smjacques/Horta-Automatizada-ESDI/imagens/800px-ATMEGA328P-PU.jpg

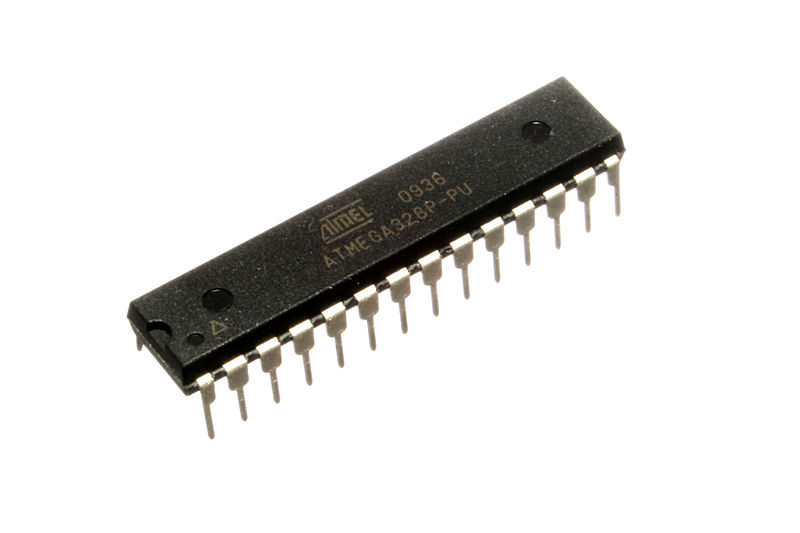
imagens/800px-ATMEGA328P-PU.jpg
