smjacques/Horta-Automatizada-ESDI/imagens/800px-Microchip_PIC24HJ32GP202.jpg

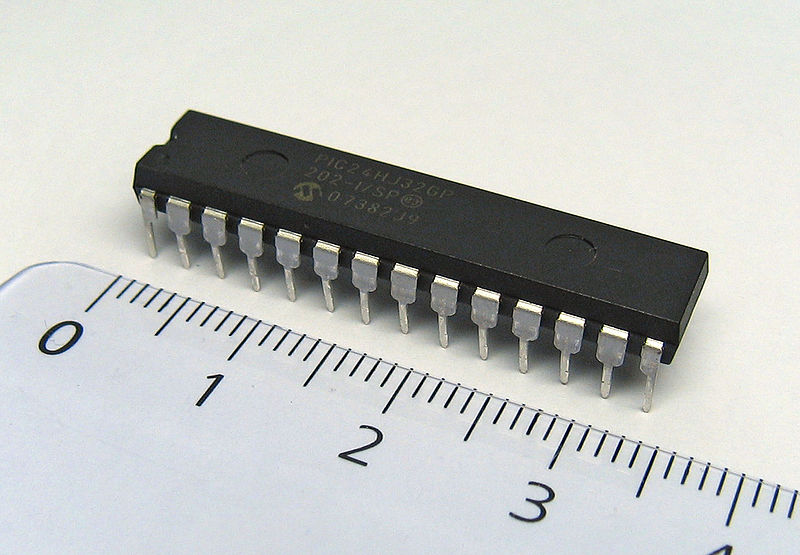
imagens/800px-Microchip_PIC24HJ32GP202.jpg
