smjacques/Horta-Automatizada-ESDI/imagens/2706173_49cf0924.jpg

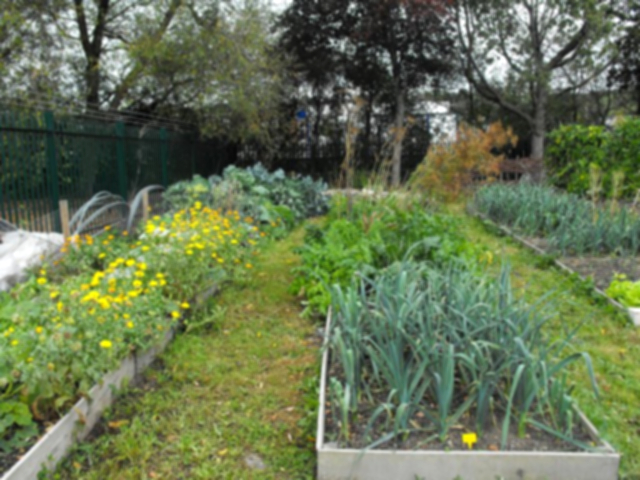
imagens/2706173_49cf0924.jpg
