smjacques/Horta-Automatizada-ESDI/imagens/aexdi.png

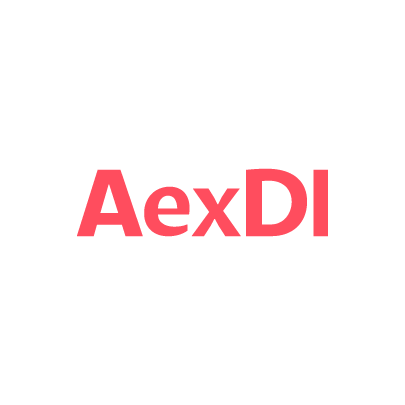
imagens/aexdi.png
