smjacques/Horta-Automatizada-ESDI/imagens/arduino_board.png

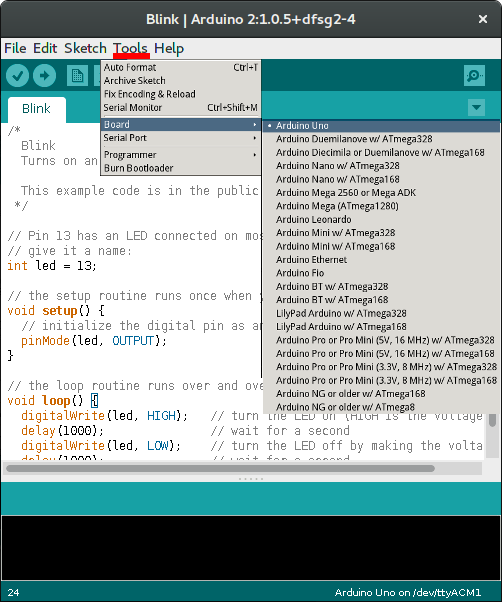
imagens/arduino_board.png
