smjacques/Horta-Automatizada-ESDI/imagens/Arduino_capa.jpg

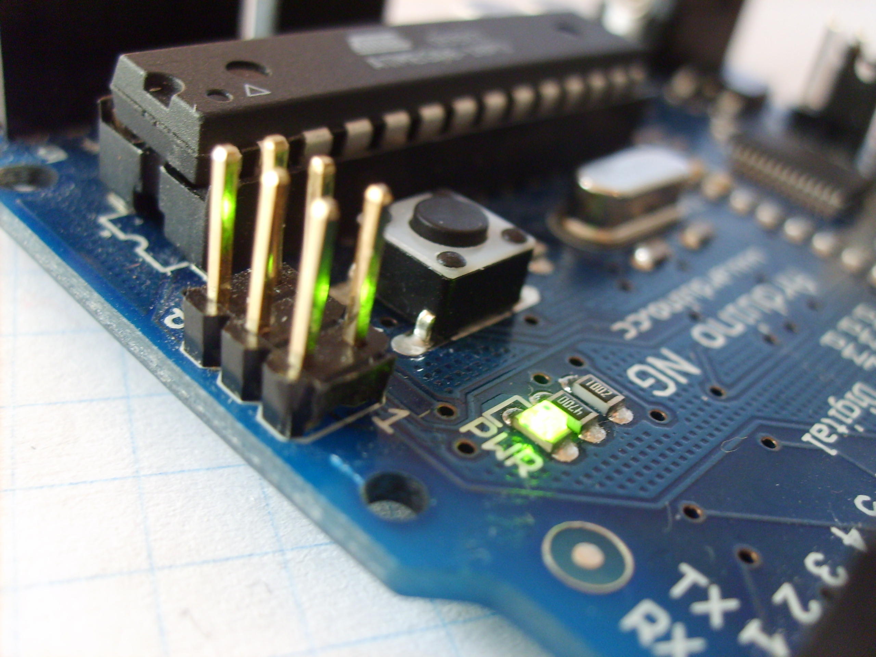
imagens/Arduino_capa.jpg
