smjacques/Horta-Automatizada-ESDI/imagens/Arduino_crystal-1.jpg

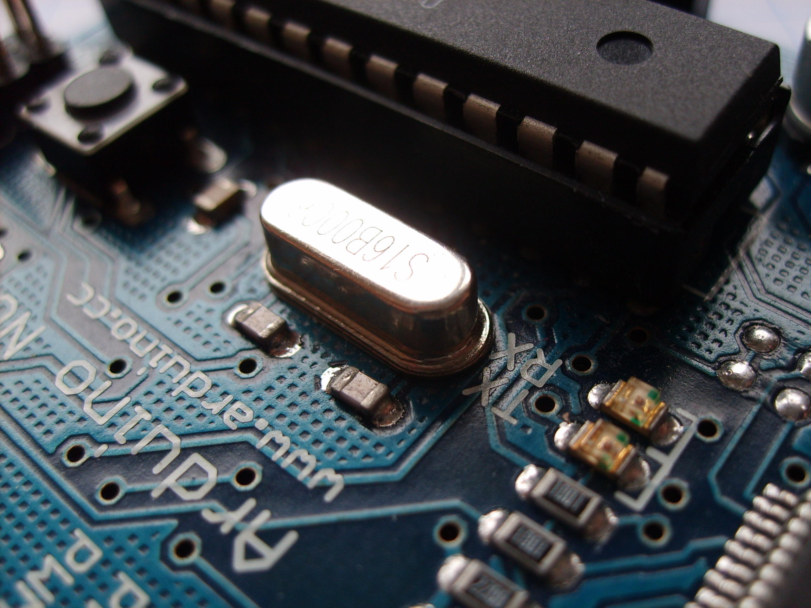
imagens/Arduino_crystal-1.jpg
