smjacques/Horta-Automatizada-ESDI/imagens/arduino_port.png

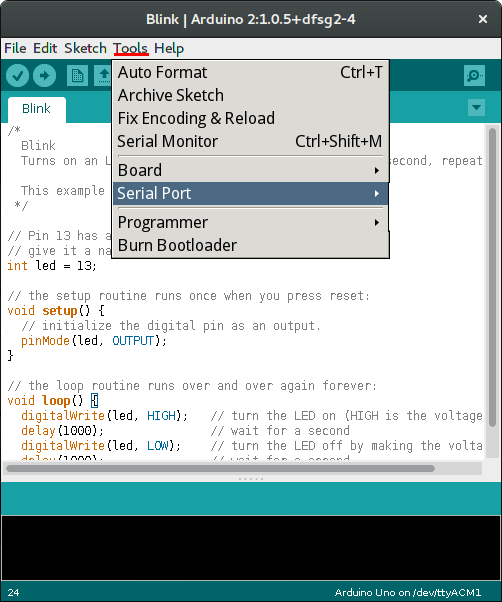
imagens/arduino_port.png
