smjacques/Horta-Automatizada-ESDI/imagens/arduinos.png

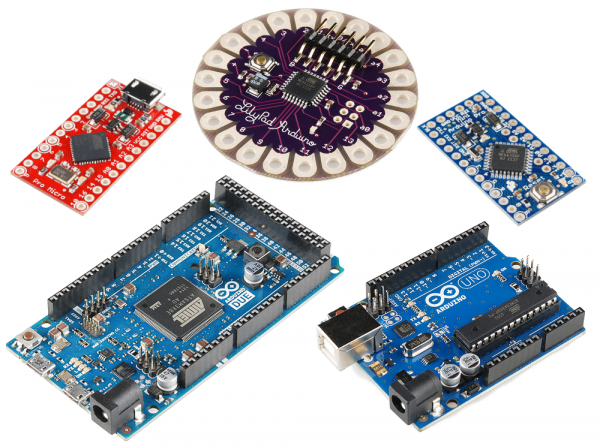
imagens/arduinos.png
