smjacques/Horta-Automatizada-ESDI/imagens/AVR_ATXMEGA_128A1.JPG

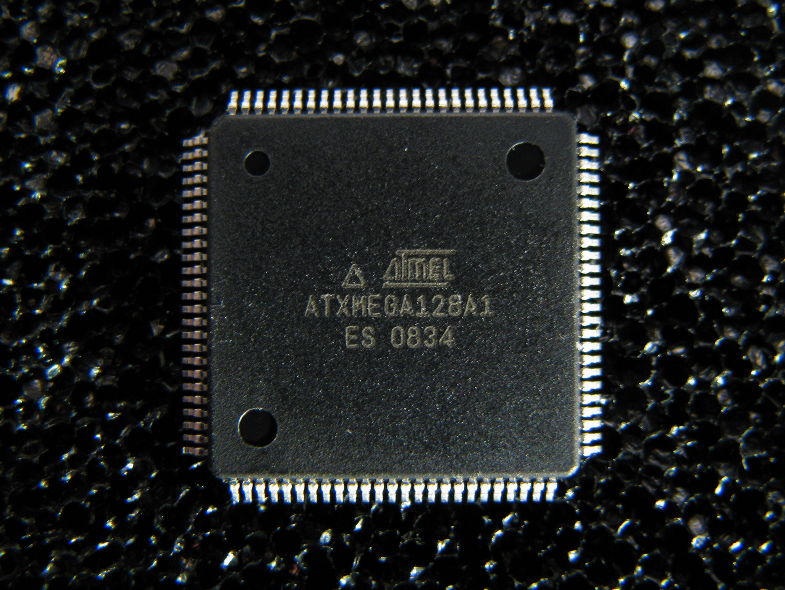
imagens/AVR_ATXMEGA_128A1.JPG
