smjacques/Horta-Automatizada-ESDI/imagens/codigo_de_cores_resistores.png

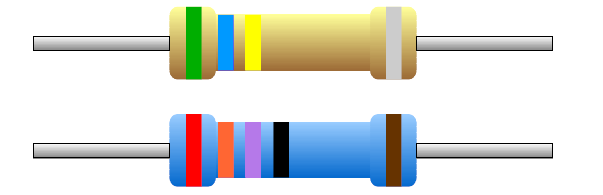
imagens/codigo_de_cores_resistores.png
