smjacques/Horta-Automatizada-ESDI/imagens/esdi.png

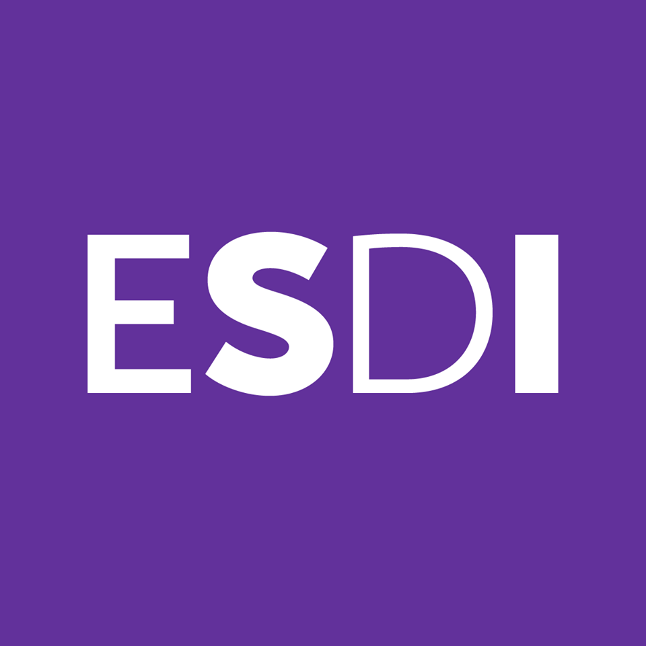
imagens/esdi.png
