smjacques/Horta-Automatizada-ESDI/imagens/green-background-2433829_1920.jpg

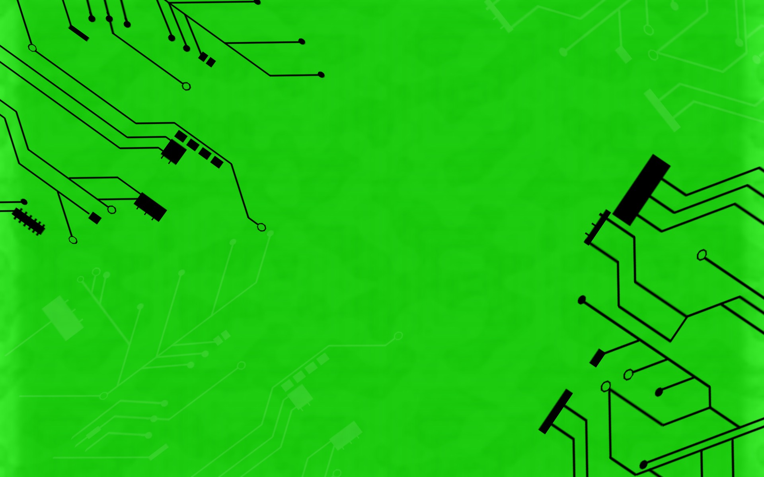
imagens/green-background-2433829_1920.jpg
