smjacques/Horta-Automatizada-ESDI/imagens/IDE.png

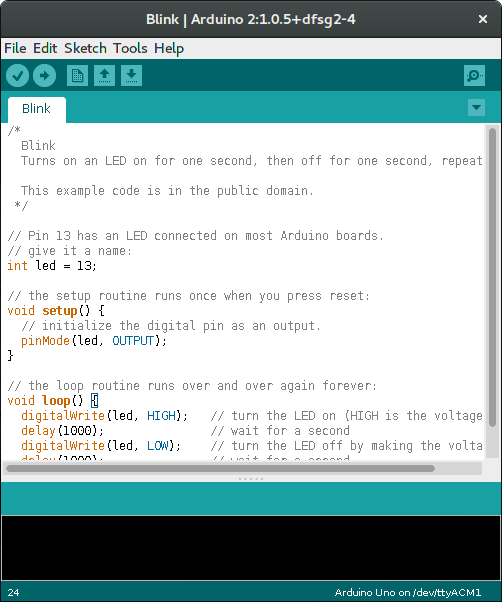
imagens/IDE.png
