smjacques/Horta-Automatizada-ESDI/imagens/images.jpeg

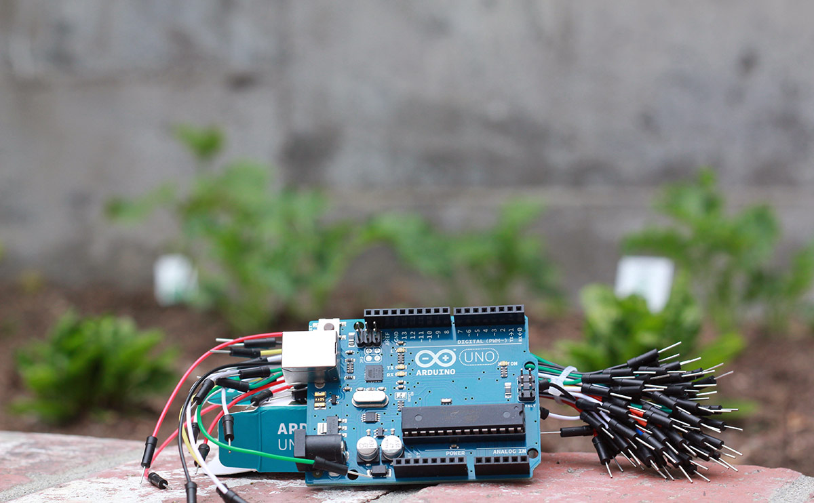
imagens/images.jpeg
