smjacques/Horta-Automatizada-ESDI/imagens/oficina_automatizada_bb.png

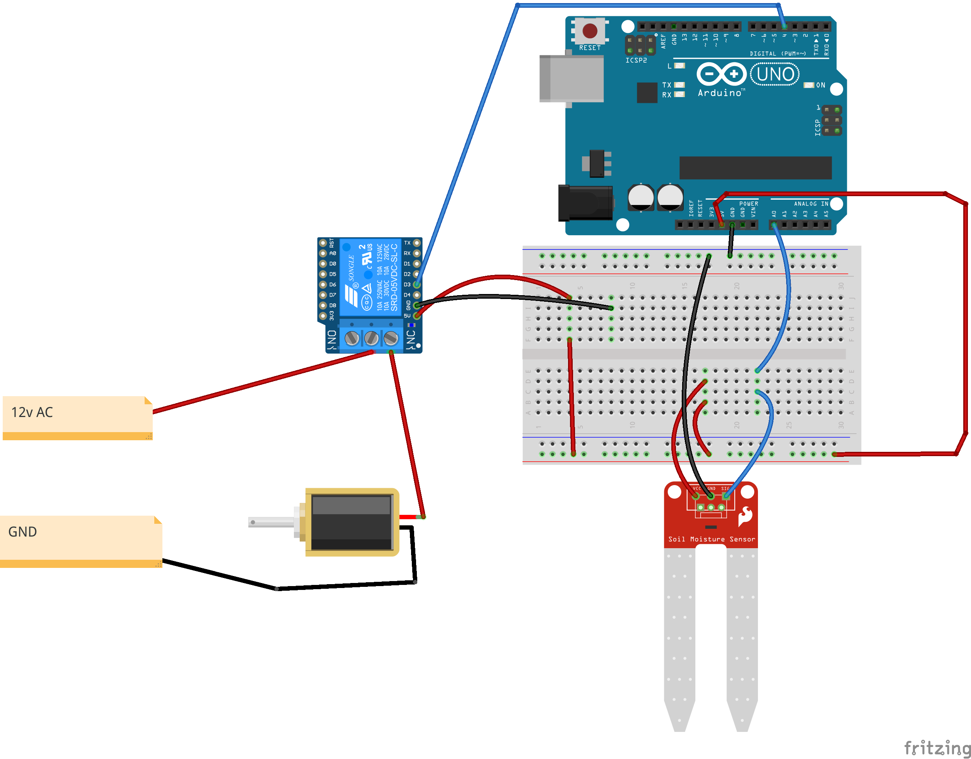
imagens/oficina_automatizada_bb.png
