smjacques/Horta-Automatizada-ESDI/imagens/ohmslaw.png

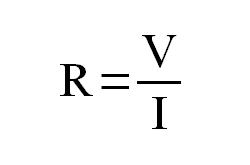
imagens/ohmslaw.png
