smjacques/Horta-Automatizada-ESDI/imagens/open file.png

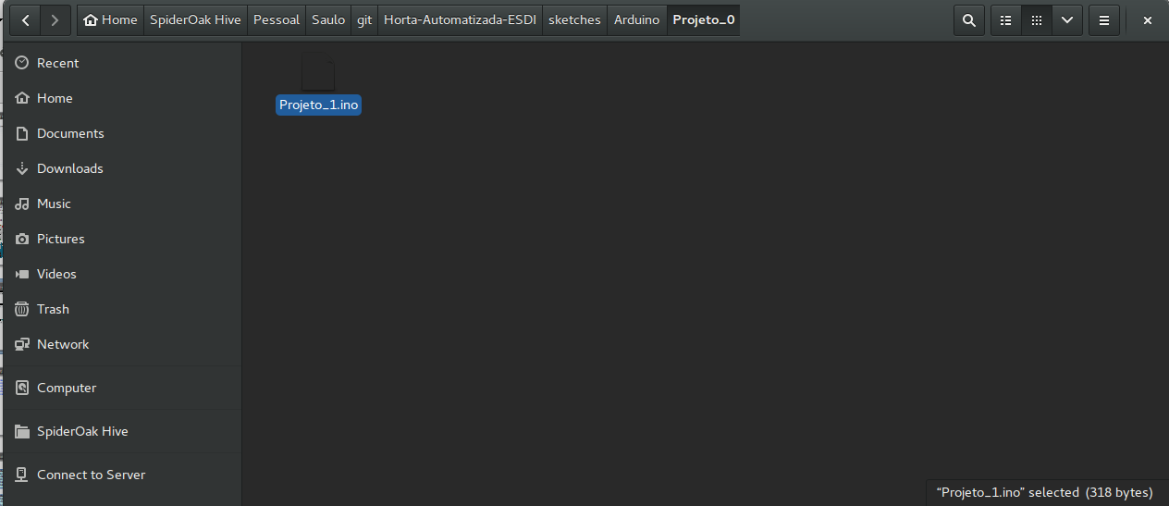
imagens/open file.png
