smjacques/Horta-Automatizada-ESDI/imagens/open folder.png

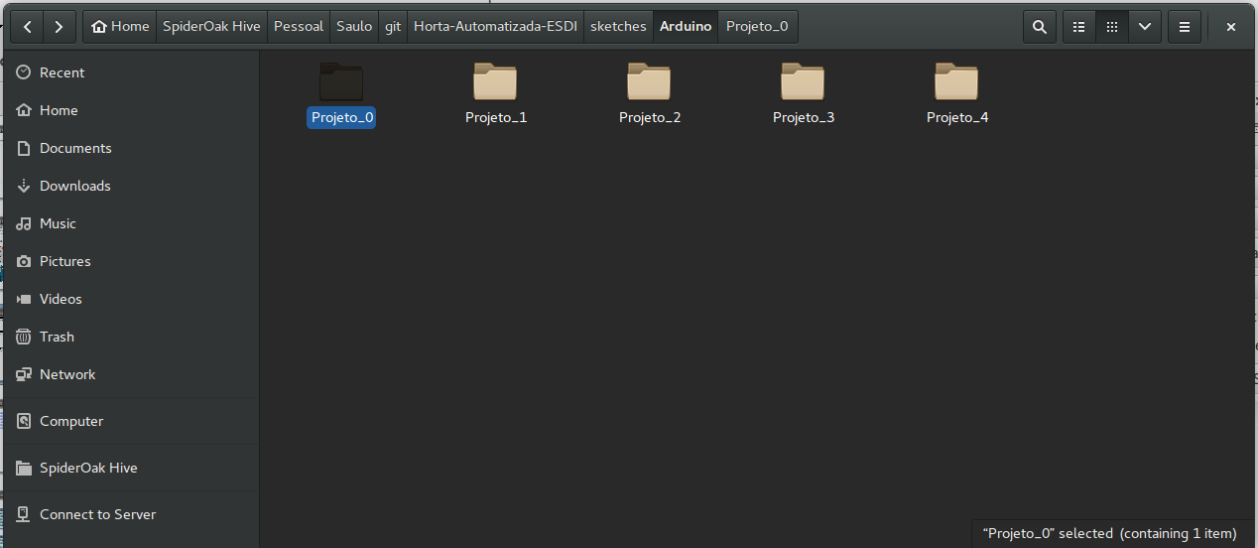
imagens/open folder.png
