smjacques/Horta-Automatizada-ESDI/imagens/prototipo_v0.1_esdi_bb.png

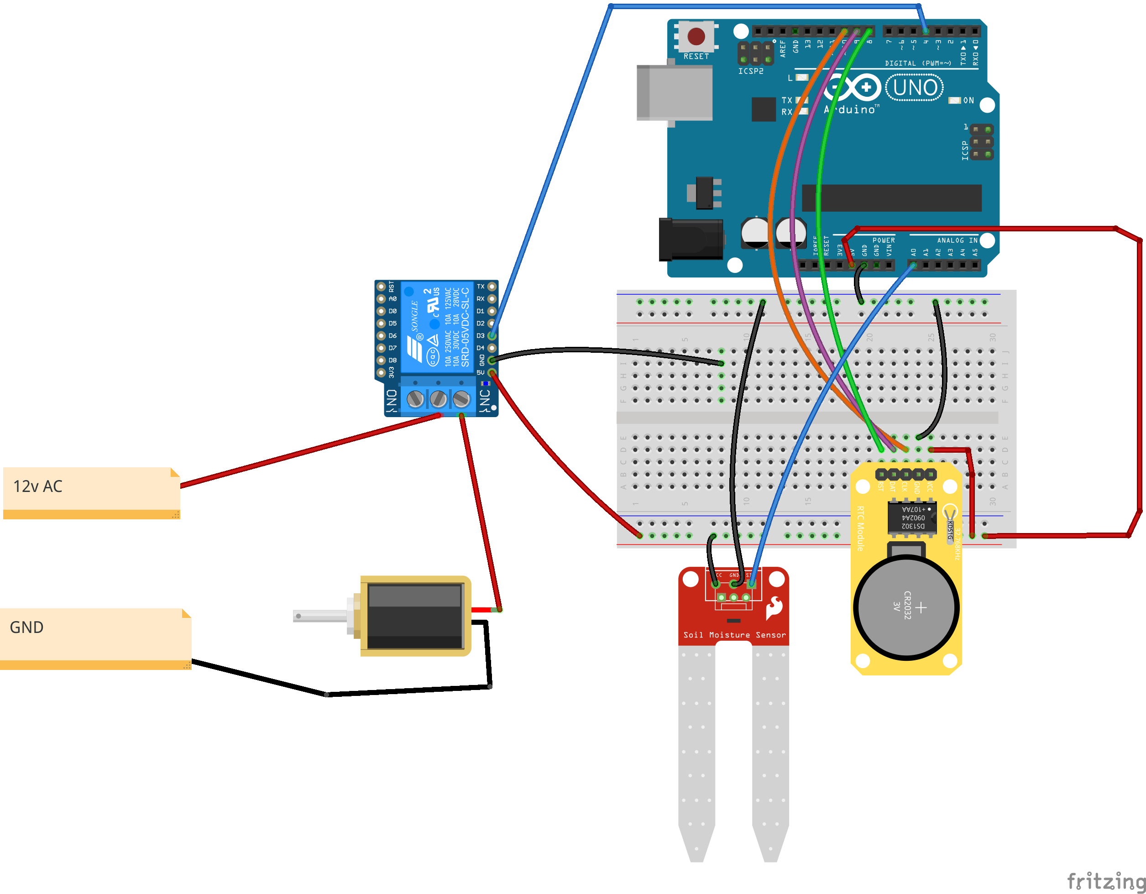
imagens/prototipo_v0.1_esdi_bb.png
