smjacques/Horta-Automatizada-ESDI/imagens/rain-2495560_1920.jpg

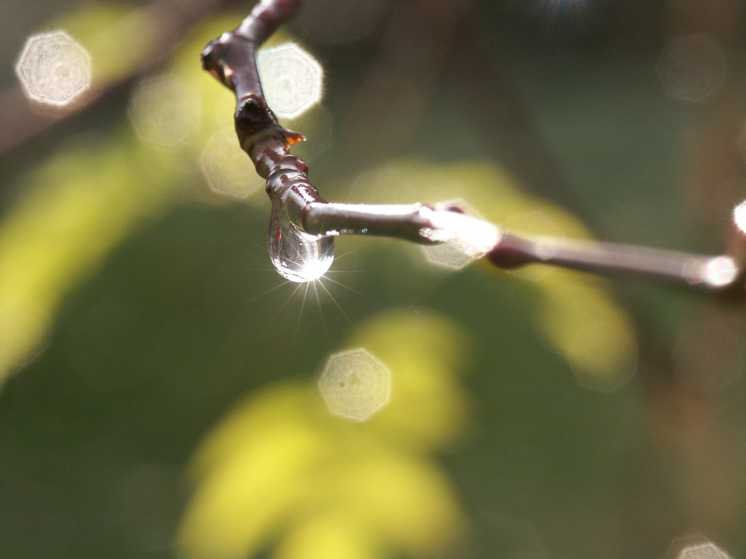
imagens/rain-2495560_1920.jpg
