smjacques/Horta-Automatizada-ESDI/imagens/Screenshot-2017-10-9 Arduino - Software.png

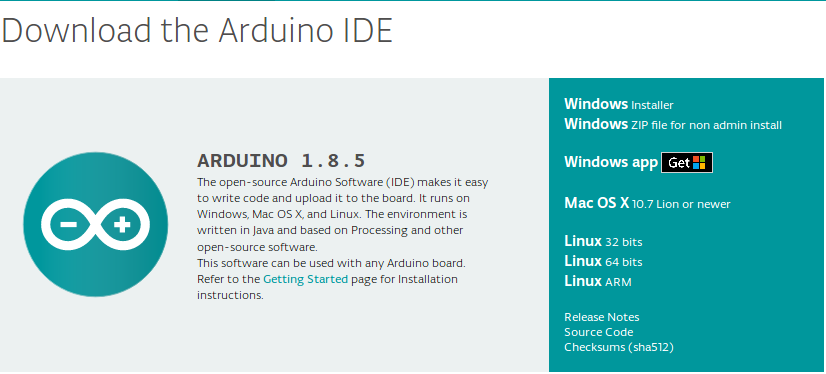
imagens/Screenshot-2017-10-9 Arduino - Software.png
