smjacques/Horta-Automatizada-ESDI/imagens/sens_umid_DIY_bb.png

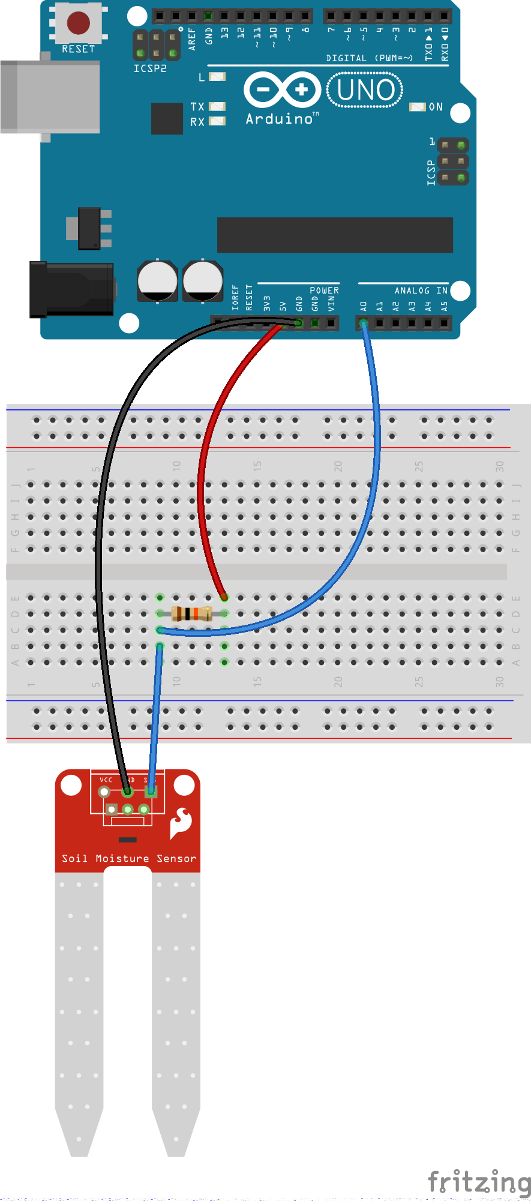
imagens/sens_umid_DIY_bb.png
