smjacques/Horta-Automatizada-ESDI/imagens/serial window_0.png

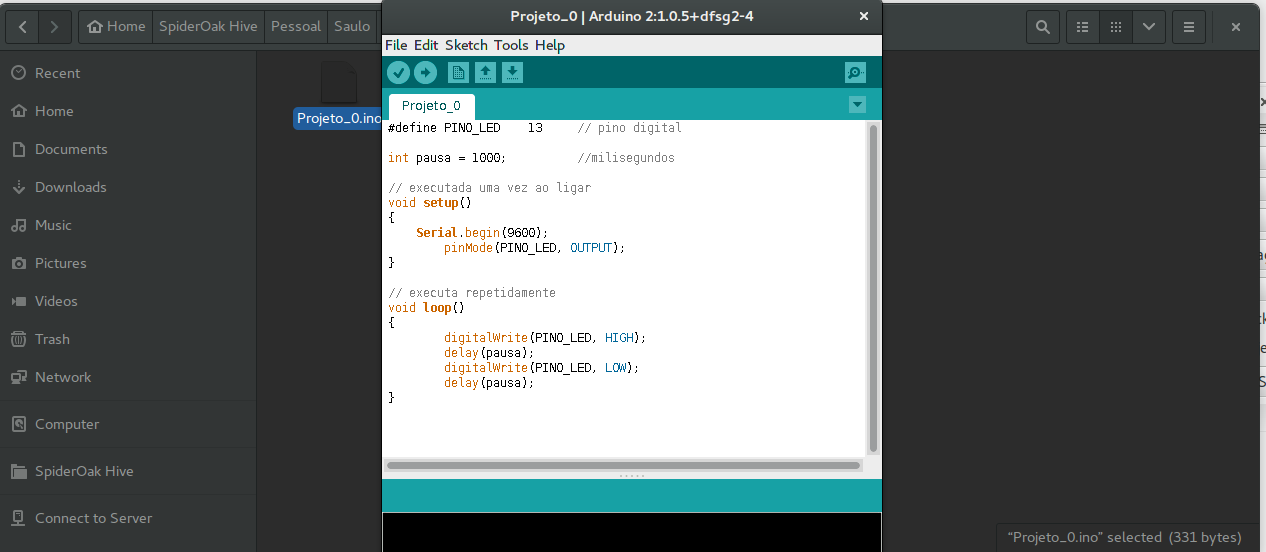
imagens/serial window_0.png
