smjacques/Horta-Automatizada-ESDI/imagens/technology_arduino_breadboard_leds_computer_science_wires_arduino_code_arduino_sdk-783699.jpg!d.jpeg

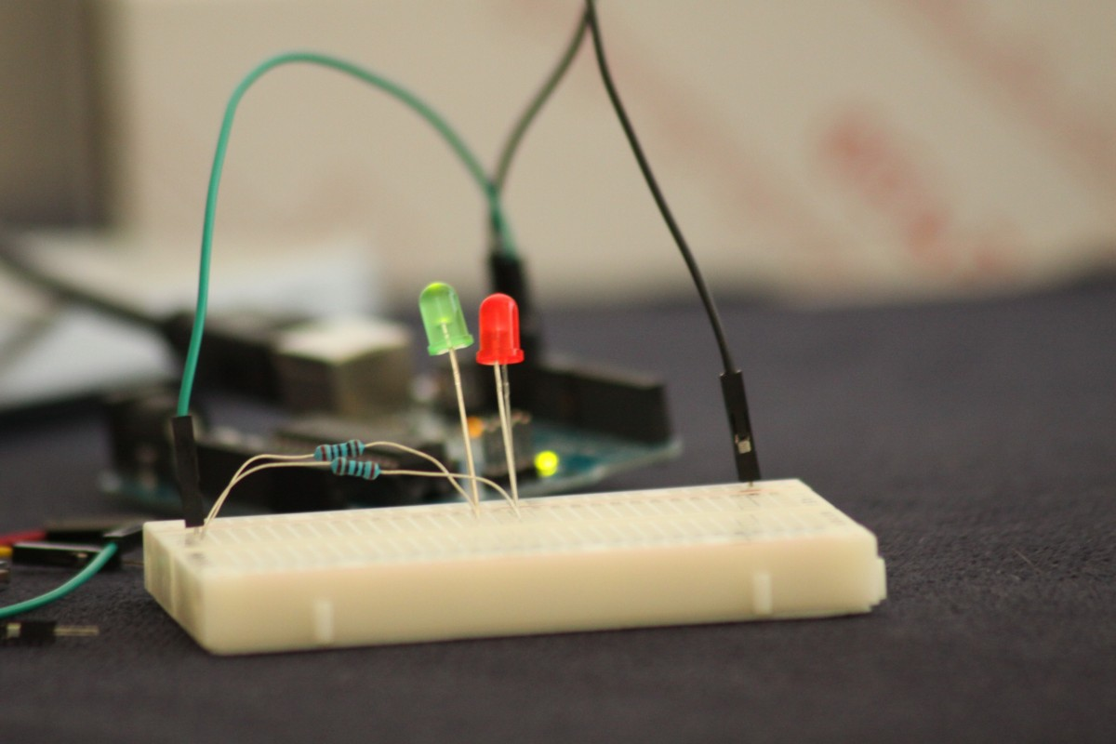
imagens/technology_arduino_breadboard_leds_computer_science_wires_arduino_code_arduino_sdk-783699.jpg!d.jpeg
