smjacques/Horta-Automatizada-ESDI/imagens/umidade_simples.jpg

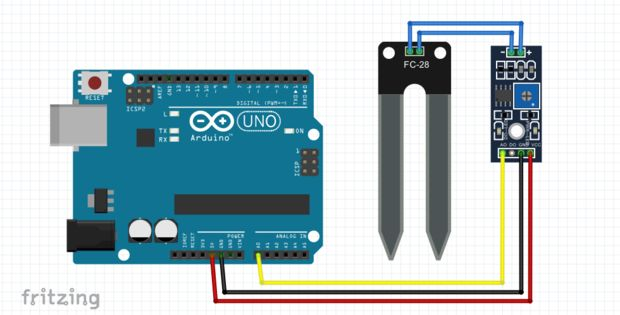
imagens/umidade_simples.jpg
