smjacques/Horta-Automatizada-ESDI/imagens/valvula-solenoide-34-saida-mang-90-1102202412v-D_NQ_NP_22929-MLB20239695169_022015-O.jpg

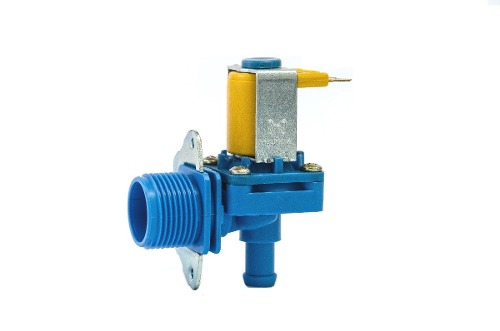
imagens/valvula-solenoide-34-saida-mang-90-1102202412v-D_NQ_NP_22929-MLB20239695169_022015-O.jpg
