smjacques/Horta-Automatizada-ESDI/imagens/Watering-Nature-Dripping-Garden-Water-Drops-Drops-175714.jpg

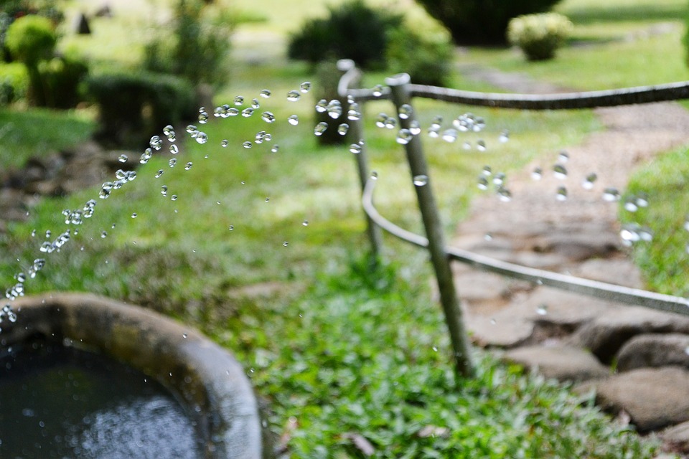
imagens/Watering-Nature-Dripping-Garden-Water-Drops-Drops-175714.jpg
