smjacques/Horta-Automatizada-ESDI/issue img/serial_print_1.png

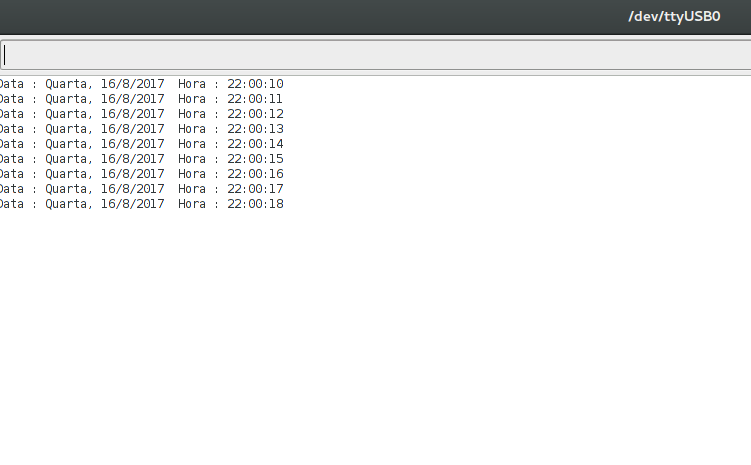
issue img/serial_print_1.png
