smjacques/Horta-Automatizada-ESDI/issue img/serial_print_2.png

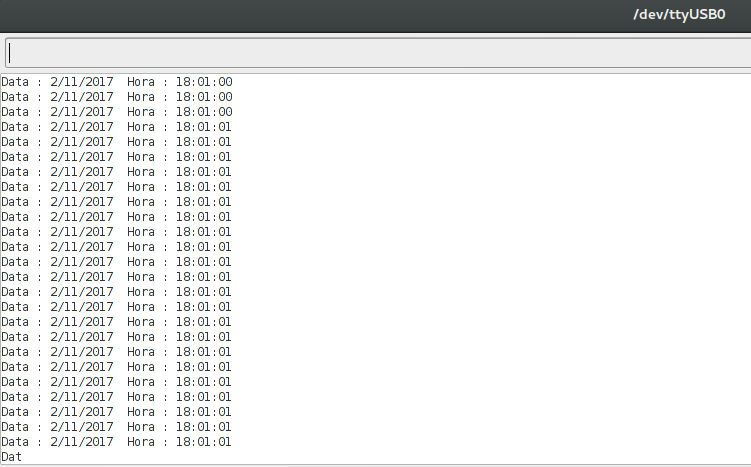
issue img/serial_print_2.png
